rodan/solar-sensor/firmware_avr/drivers/ir_remote.h

#ifndef __IR_REMOTE_H__
#define __IR_REMOTE_H__

#include <stdint.h>
#include <avr/io.h>
#include "port_config.h"

/*
// the ir sensor is tied to PD2
#define IR          0b00000100
#define IR_DDR      DDRD
#define IR_PIN      PIND
*/

#define USECPERTICK 50
#define RAWBUF 28

// Marks tend to be 100us too long, and spaces 100us too short
// when received due to sensor lag.
#define MARK_EXCESS 100

// information for the interrupt handler
typedef struct {
    uint8_t rcvstate;           // state machine
    uint16_t timer;             // state timer, counts 50uS ticks.
    uint16_t rawbuf[RAWBUF];    // raw data
    uint8_t rawlen;             // counter of entries in rawbuf
} irparams_t;

// Results returned from the decoder
typedef struct {
    int decode_type;            // NEC, SONY, RC5, UNKNOWN
    uint32_t value;             // Decoded value
    int bits;                   // Number of bits in decoded value
    volatile uint16_t *rawbuf;  // Raw intervals in .5 us ticks
    int rawlen;                 // Number of records in rawbuf.
} decode_results;

extern volatile irparams_t irparams;
extern decode_results results;

#define TOLERANCE 25            // percent tolerance in measurements
#define LTOL (1.0 - TOLERANCE/100.)
#define UTOL (1.0 + TOLERANCE/100.)

#define _GAP 5000               // Minimum map between transmissions
#define GAP_TICKS (_GAP/USECPERTICK)

#define TICKS_LOW(us) (int) (((us)*LTOL/USECPERTICK))
#define TICKS_HIGH(us) (int) (((us)*UTOL/USECPERTICK + 1))

#define IR_CCR    (MCLK_FREQ * USECPERTICK / 1000000)

// IR detector output is active low
#define MARK  0
#define SPACE 1

// receiver states
#define STATE_IDLE     2
#define STATE_MARK     3
#define STATE_SPACE    4
#define STATE_STOP     5

#define ERR 0
#define DECODED 1

//#define NEC 1
//#define SONY 2
#define RC5 3
//#define RC6 4
//#define DISH 5
//#define SHARP 6
#define UNKNOWN -1

#define MIN_RC5_SAMPLES 11
#define RC5_T1		889

// Use FNV hash algorithm: http://isthe.com/chongo/tech/comp/fnv/#FNV-param
#define FNV_PRIME_32 16777619
#define FNV_BASIS_32 2166136261UL

void ir_init(void);
void ir_halt(void);
void ir_resume(void);
uint8_t ir_decode(decode_results * results);
uint8_t decode_rc5(decode_results * results);
uint8_t decode_hash(decode_results * results);
uint16_t get_rc_level(decode_results * results, int *offset, int *used,
                      const int t1);
uint8_t compare(const uint16_t oldval, const uint16_t newval);
uint8_t MATCH(const uint16_t measured, const uint16_t desired);

#ifdef F_CPU
#define SYSCLOCK F_CPU
#else
#define SYSCLOCK 16000000
#endif

#define TIMER_RESET
#define TIMER_ENABLE_PWM     (TCCR2A |= _BV(COM2B1))
#define TIMER_DISABLE_PWM    (TCCR2A &= ~(_BV(COM2B1)))
#define TIMER_ENABLE_INTR    (TIMSK2 = _BV(OCIE2A))
#define TIMER_DISABLE_INTR   (TIMSK2 = 0)
#define TIMER_INTR_NAME      TIMER2_COMPA_vect
#define TIMER_CONFIG_KHZ(val) ({ \
  const uint8_t pwmval = SYSCLOCK / 2000 / (val); \
  TCCR2A = _BV(WGM20); \
  TCCR2B = _BV(WGM22) | _BV(CS20); \
  OCR2A = pwmval; \
  OCR2B = pwmval / 3; \
})
#define TIMER_COUNT_TOP      (SYSCLOCK * USECPERTICK / 1000000)
#if (TIMER_COUNT_TOP < 256)
#define TIMER_CONFIG_NORMAL() ({ \
  TCCR2A = _BV(WGM21); \
  TCCR2B = _BV(CS20); \
  OCR2A = TIMER_COUNT_TOP; \
  TCNT2 = 0; \
})
#else
#define TIMER_CONFIG_NORMAL() ({ \
  TCCR2A = _BV(WGM21); \
  TCCR2B = _BV(CS21); \
  OCR2A = TIMER_COUNT_TOP / 8; \
  TCNT2 = 0; \
})
#endif

#endif
